moonbeaminteractive/feedback-vest/assets/circuit.jpg

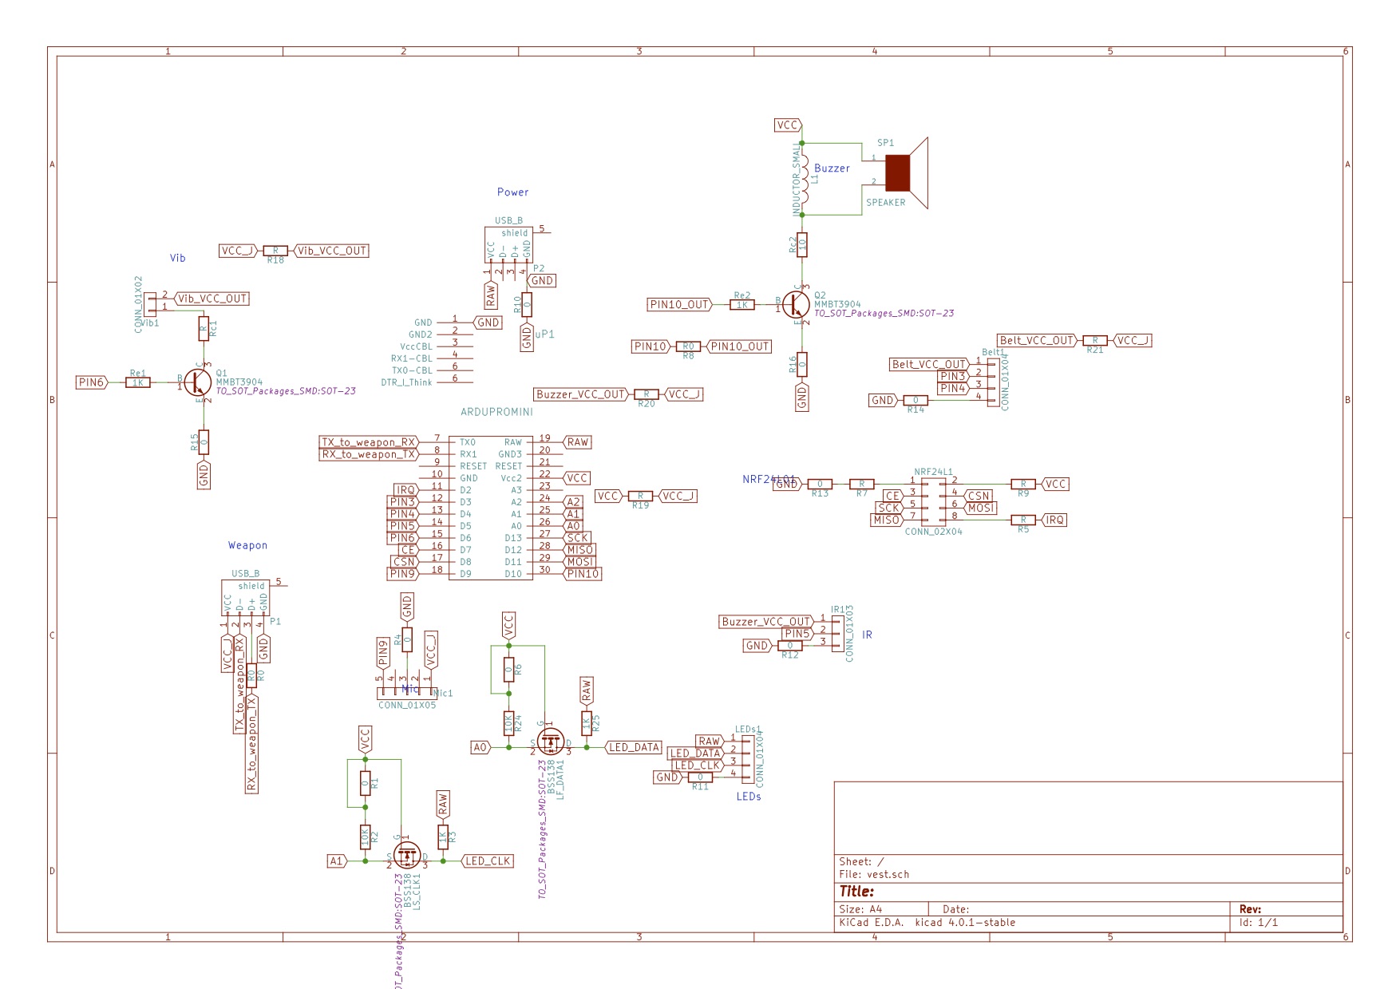
assets/circuit.jpg
