moonbeaminteractive/feedback-vest/models/Images/IR sensors/20161214_173102.jpg

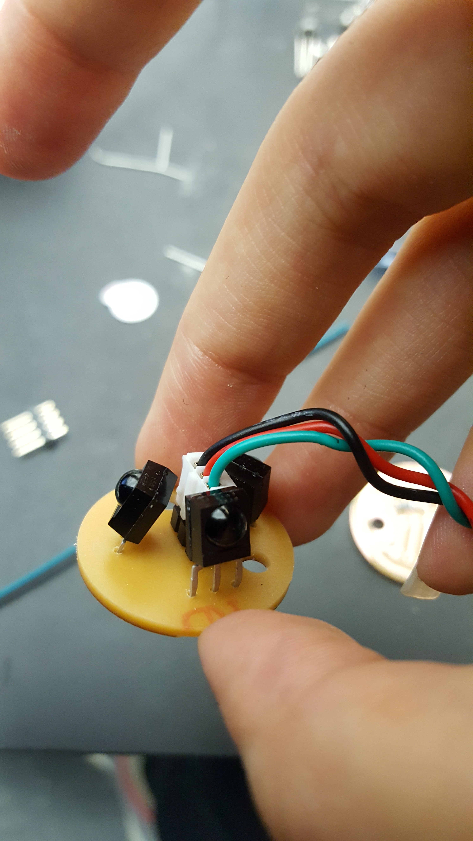
models/Images/IR sensors/20161214_173102.jpg
