moonbeaminteractive/feedback-vest/models/Images/main board/20161214_191831.jpg

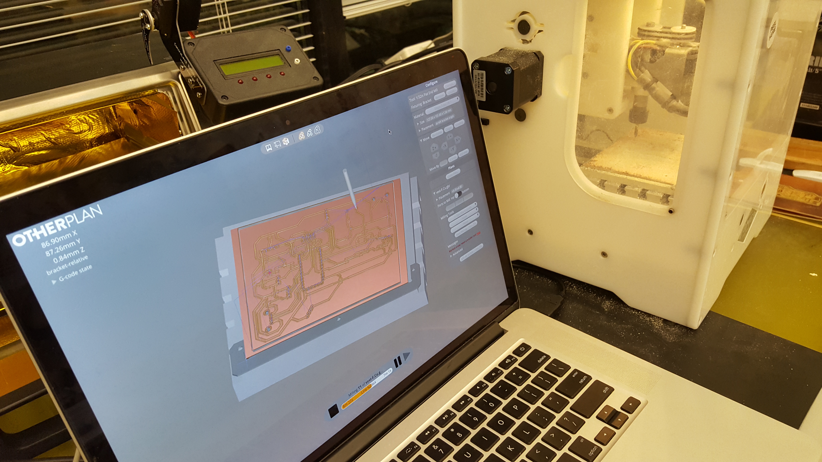
models/Images/main board/20161214_191831.jpg
