moonbeaminteractive/feedback-vest/models/Images/main board/20161214_192655.jpg

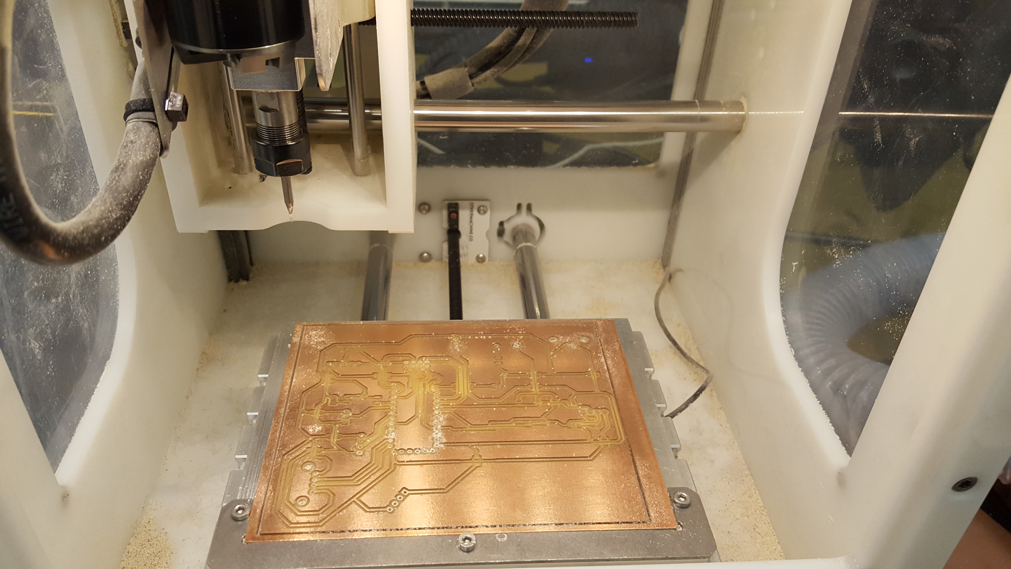
models/Images/main board/20161214_192655.jpg
