moonbeaminteractive/feedback-vest/models/Images/main board/20161215_002419.jpg

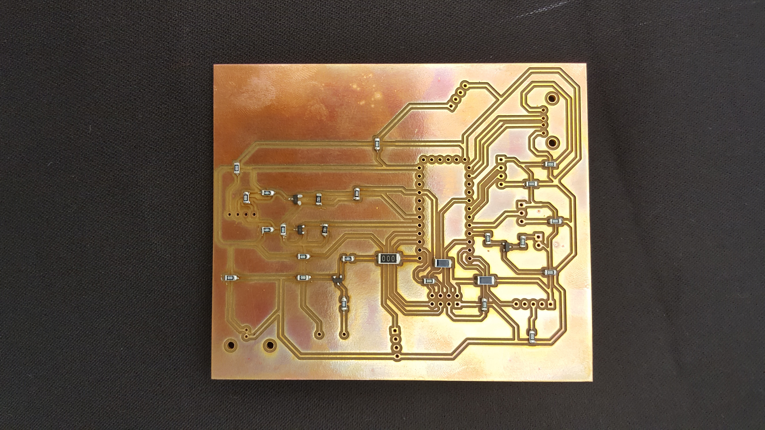
models/Images/main board/20161215_002419.jpg
