moonbeaminteractive/feedback-vest/models/Images/main board/20161215_120049.jpg

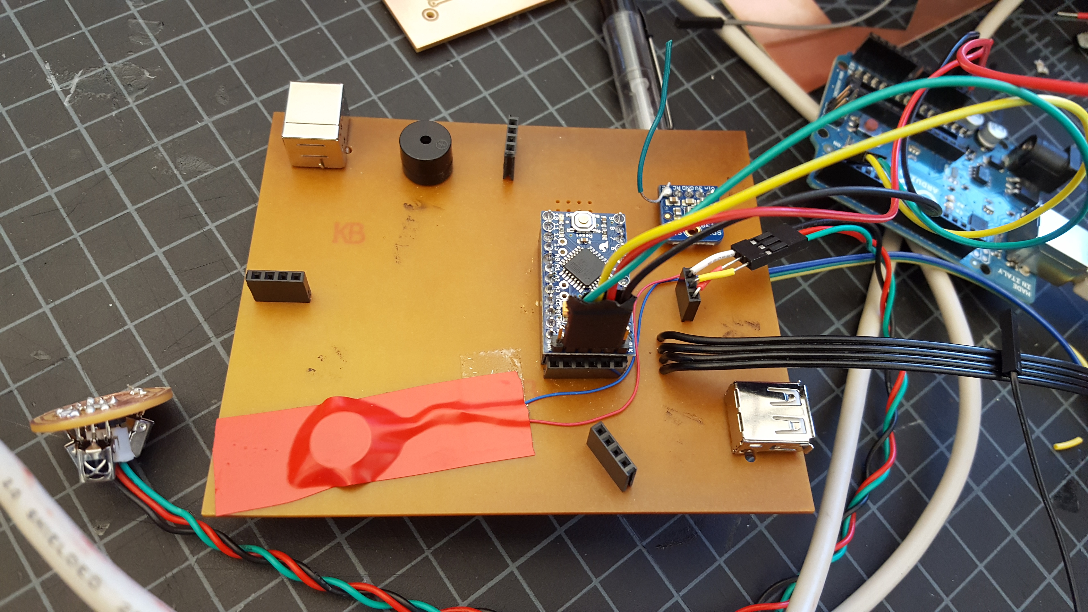
models/Images/main board/20161215_120049.jpg
