moonbeaminteractive/feedback-vest/models/Images/main board/20161215_123714.jpg

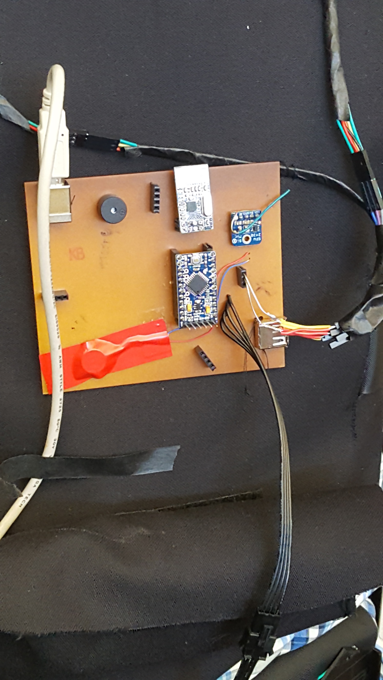
models/Images/main board/20161215_123714.jpg
