moonbeaminteractive/feedback-vest/models/Images/vest/20161215_034244.jpg

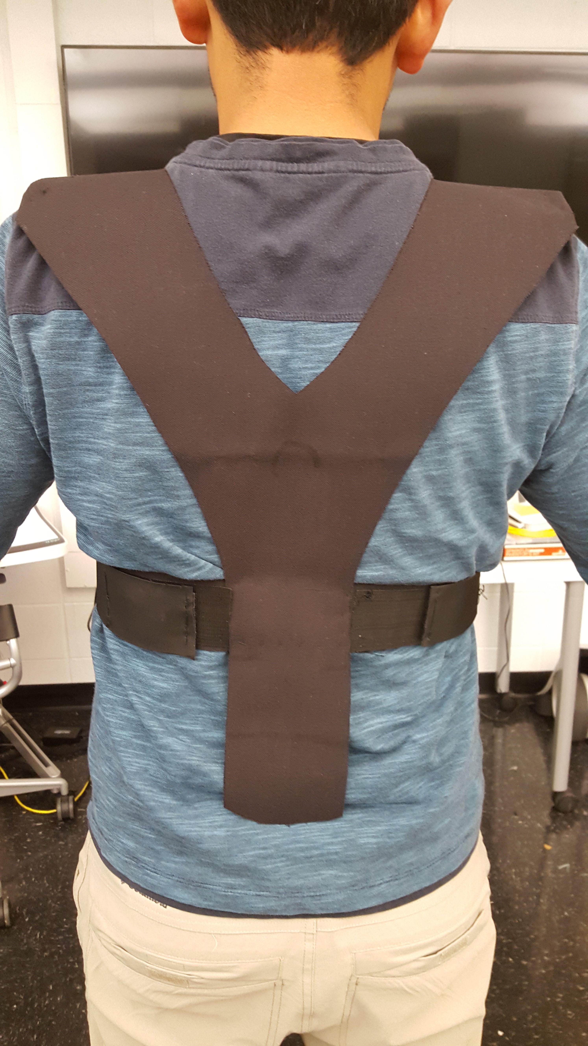
models/Images/vest/20161215_034244.jpg
