moonbeaminteractive/feedback-vest/models/Images/vest/20161215_035906.jpg

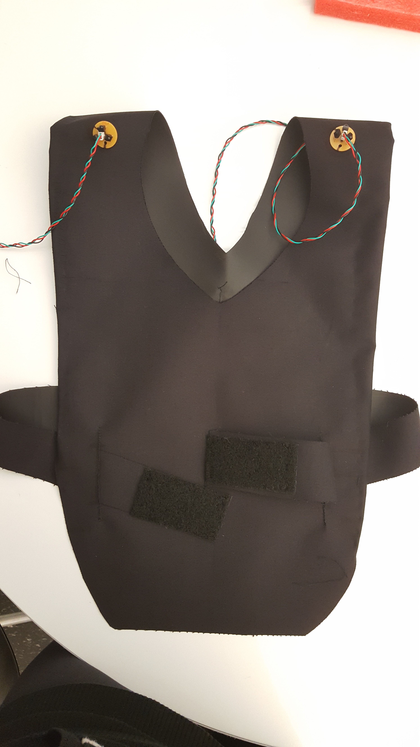
models/Images/vest/20161215_035906.jpg
