moonbeaminteractive/feedback-vest/models/Images/vest/20161215_035917.jpg

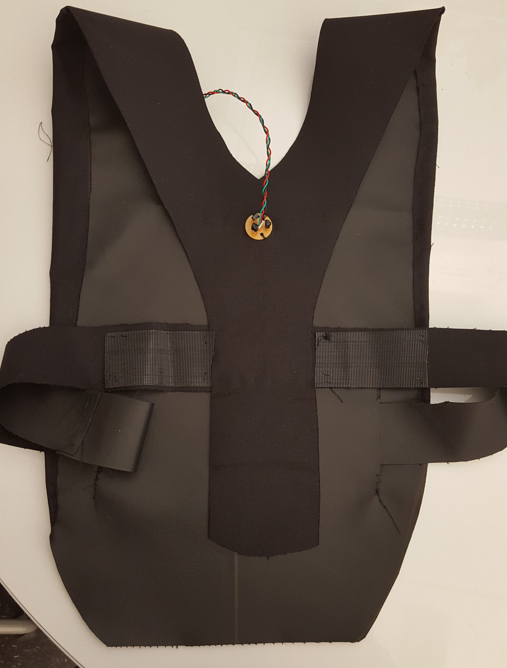
models/Images/vest/20161215_035917.jpg
