moonbeaminteractive/feedback-vest/models/Images/whole/20161215_122753.jpg

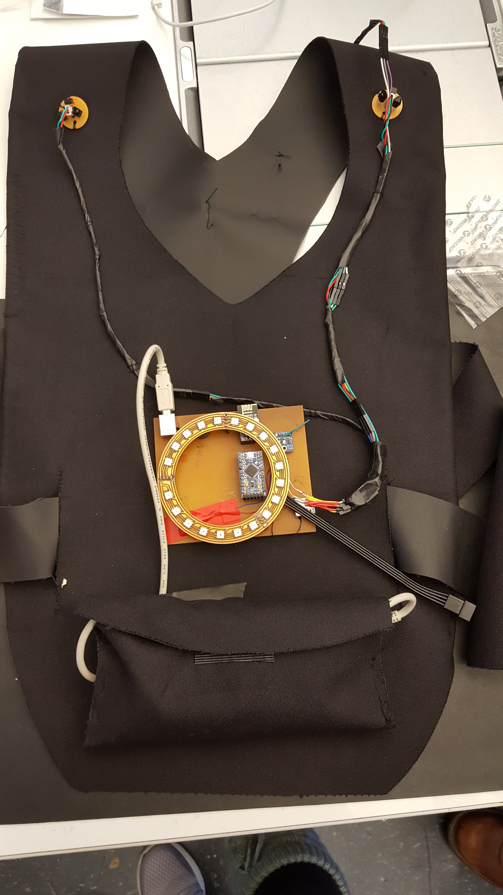
models/Images/whole/20161215_122753.jpg
