moonbeaminteractive/feedback-vest/models/Images/whole/20161215_125622.jpg

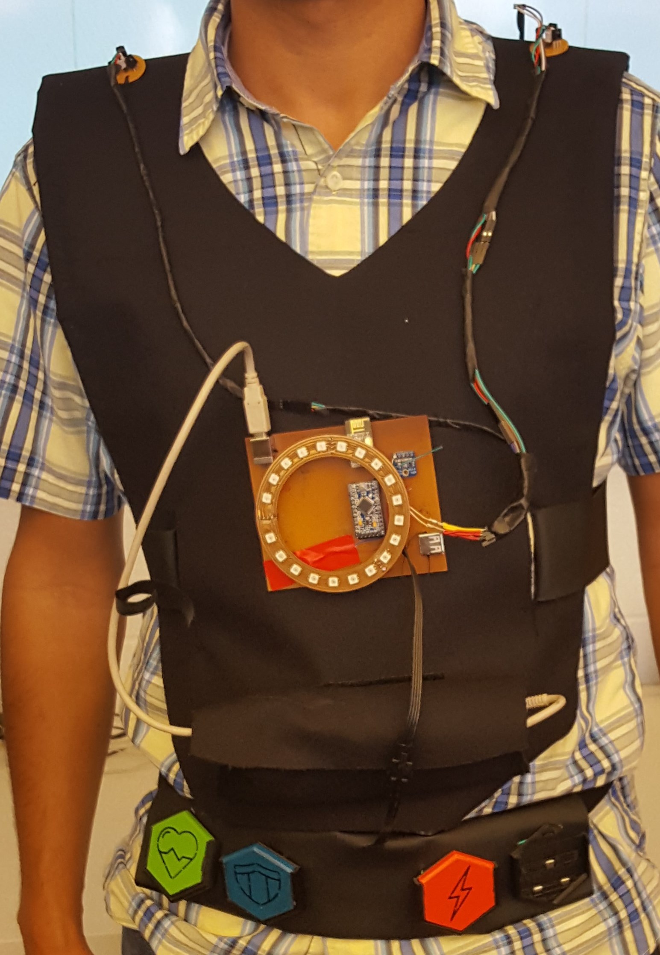
models/Images/whole/20161215_125622.jpg
