moonbeaminteractive/feedback-vest/models/Images/IR sensors/20161214_172617.jpg

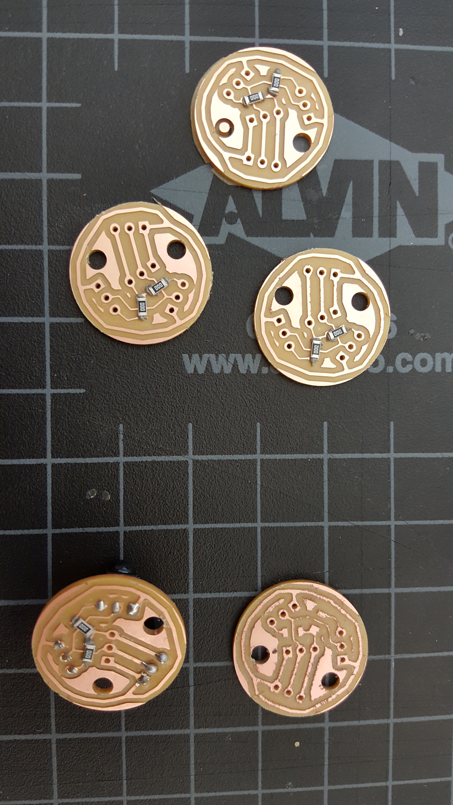
models/Images/IR sensors/20161214_172617.jpg
