moonbeaminteractive/feedback-vest/models/Images/LED Ring/20161213_224332.jpg

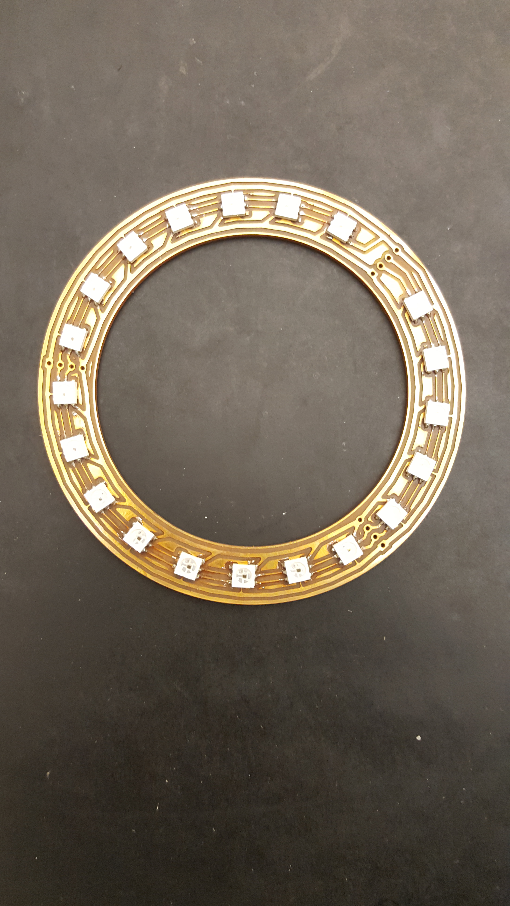
models/Images/LED Ring/20161213_224332.jpg
