moonbeaminteractive/feedback-vest/models/Images/main board/20161215_122745.jpg

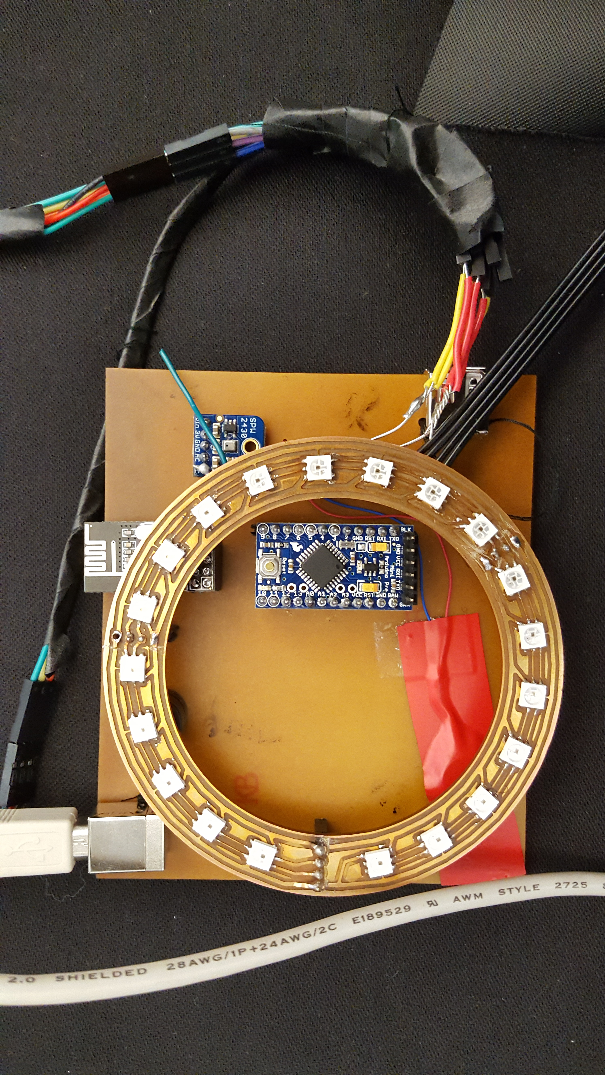
models/Images/main board/20161215_122745.jpg
